rnat697/smartEnergyMonitor_T15/Final Version/Hardware/Draft1.asc

C1: cap; 2.34n
C2: cap; 10n
C3: cap; 2.1n
Cf1: cap; 15.915n
Cf2: cap; 2.34n
Cf3: cap; 15.915n
Cf4: cap; 2.1n
Cin1: cap; 47µ; Rser=0.001
Cout1: cap; 10µ; Rser=0.001
D1: diode; 1N4148
Lload1: ind; 4mH
R1: res; 3.3k
R1a: res; 56k
R1b: res; 2.7k
R2: res; 3.3k
R3: res; 6.8k
R4: res; 6.8k
R5: res; 4.4k
R6: res; 6.8k
R7: res; 6.8k
R8: res; 6.8k
R13: res; 39k
R15: res; 27k
Reg1: LT1085-5
Rf1: res; 1k
Rf2: res; 1k
Rin1: res; 33
RL1: res; 100
Rload1: res; 17
Rs1: res; 1
Rs2: res; 1
U1: opamp2; LM324
U2: opamp2; LM324
U3: opamp2; LM324
U4: opamp2; LM324
U5: opamp2; LM324
Vsupply1: voltage; SINE(0 21.78 500); AC 1
Named nets: 0, Vac, 2V1, 5VDis, Vin, Vis, Vout, VvsOUT, VisOUT, Vvs, Vout2
Simulation Commands
************************************************
COMPSYS/ELECTENG 209 
Energy Monitor Schematic - Group 15
 
20/10/2021
************************************************
Voltage Sens
5V regulator circuit design
Offset voltage(5V) supplied to the Op-Amp
Voltage zero crossing detector circuit design
.lib LM324.lib
OpAmps & Filters
;tran 0 0.2 0 0.01
Vvs has initial resistance which is why its different
R1 thevenin not considered as resistor too small
Current Sens
2.1V DC Voltage Divider with Buffer
12.6 - 15.4 Vrms
Voltage comparators
VD of
27k/39k
Current Sensor Opamp
Voltage Sensor Opamp
.ic V(Vin) = 10
.ac dec 30 1 1Meg
V(visout)/V(Vis) equation for simulation
V(vvsout)/V(Vvs) equation for simulation
